dslik/ttam/stamps/1071A/1071-0101/latest/pcb_top.png

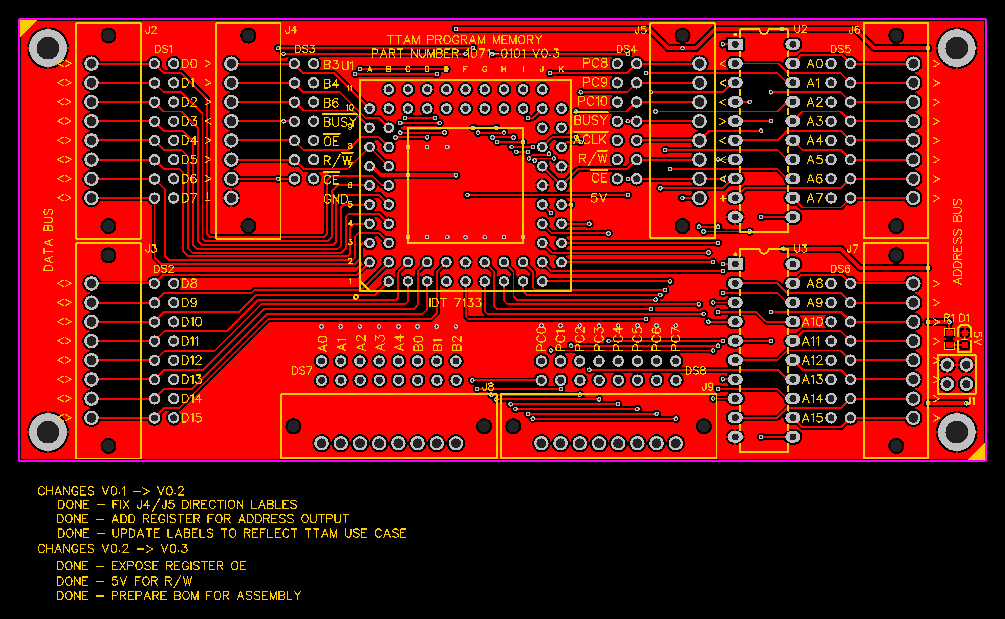
stamps/1071A/1071-0101/latest/pcb_top.png
