dslik/ttam/stamps/1072A/1072-0101/latest/pcb_top.png

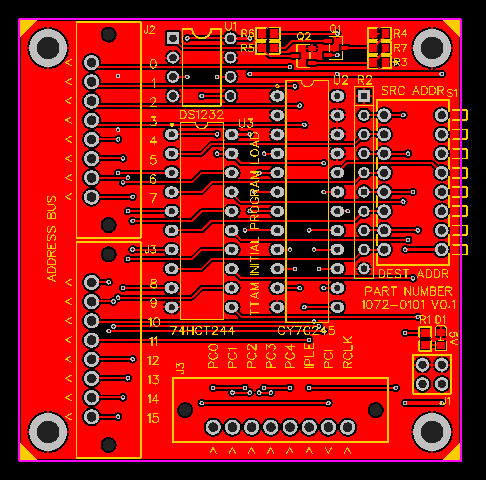
stamps/1072A/1072-0101/latest/pcb_top.png
