dslik/ttam/stamps/1073A/1073-0101/latest/pcb_top.png

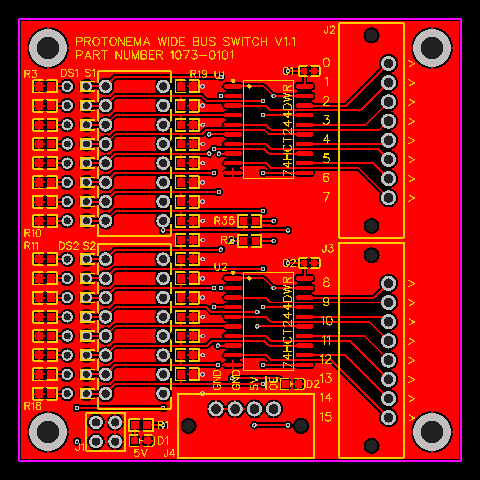
stamps/1073A/1073-0101/latest/pcb_top.png
