dslik/ttam/stamps/1074A/1074-0101/latest/pcb_top.png

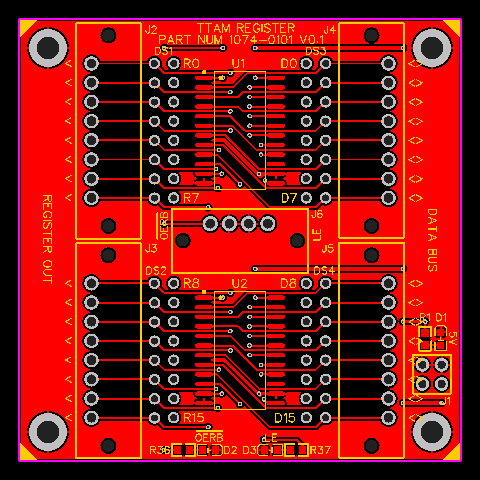
stamps/1074A/1074-0101/latest/pcb_top.png
