dslik/ttam/stamps/1075A/1075-0101/latest/pcb_top.png

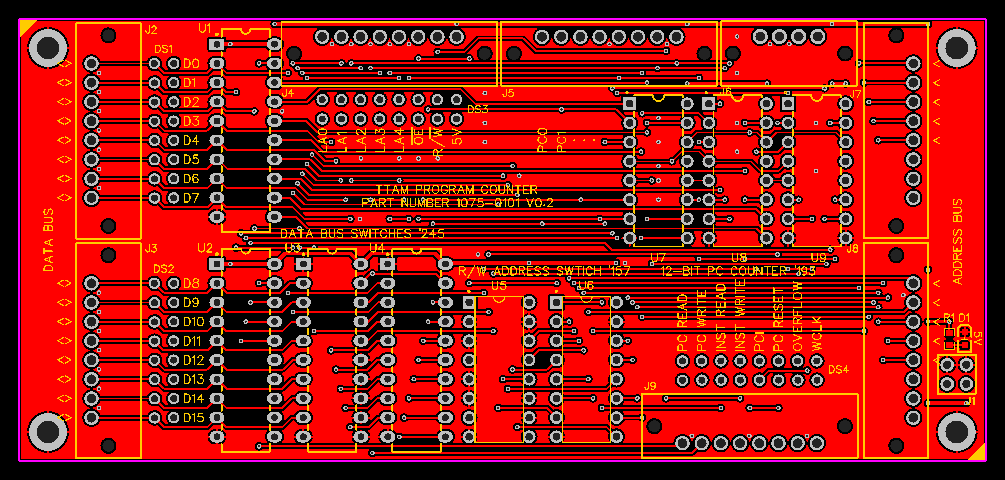
stamps/1075A/1075-0101/latest/pcb_top.png
