dslik/ttam/stamps/1076A/1076-0101/latest/pcb_top.png

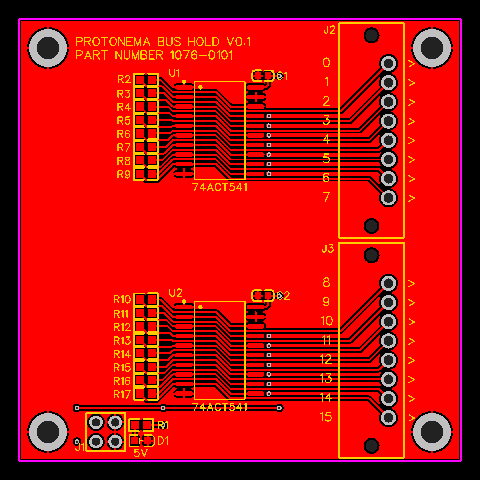
stamps/1076A/1076-0101/latest/pcb_top.png
