dslik/ttam/stamps/1077A/1077-0101/latest/pcb_top.png

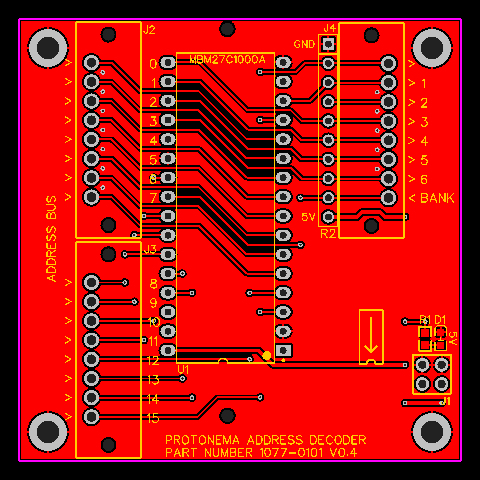
stamps/1077A/1077-0101/latest/pcb_top.png
