dslik/ttam/stamps/1078A/1078-0101/latest/pcb_top.png

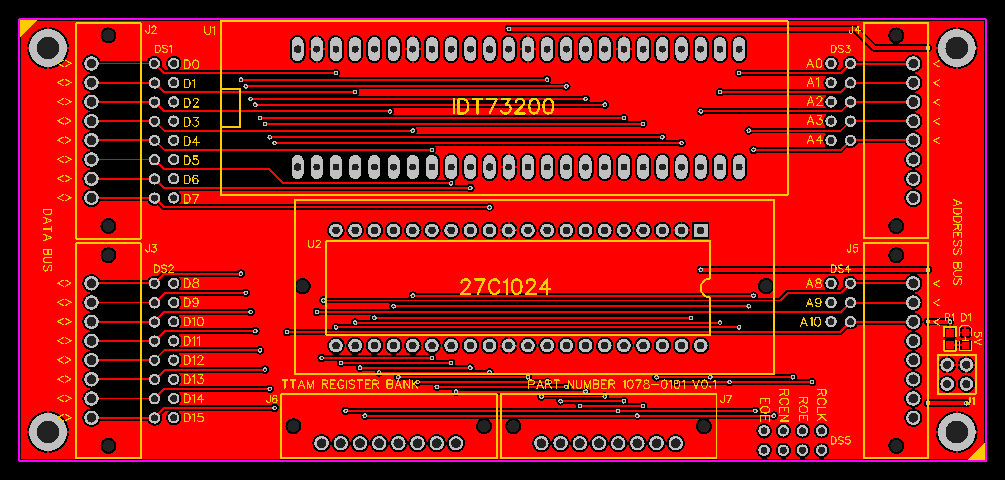
stamps/1078A/1078-0101/latest/pcb_top.png
