dslik/ttam/stamps/1079A/1079-0101/latest/pcb_top.png

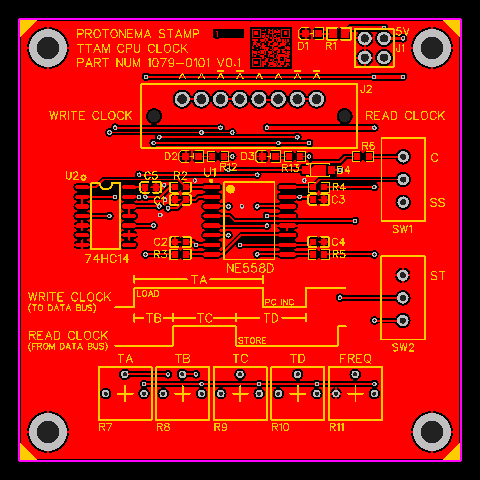
stamps/1079A/1079-0101/latest/pcb_top.png
