dslik/ttam/stamps/1080A/1080-0101/latest/pcb_bottom.png

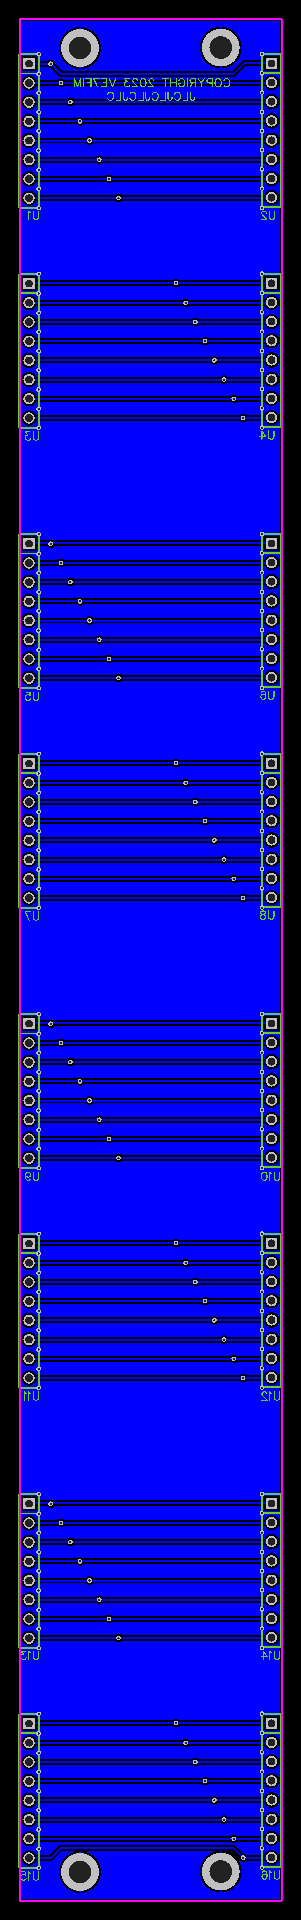
stamps/1080A/1080-0101/latest/pcb_bottom.png
