dslik/ttam/stamps/1080A/1080-0101/latest/pcb_top.png

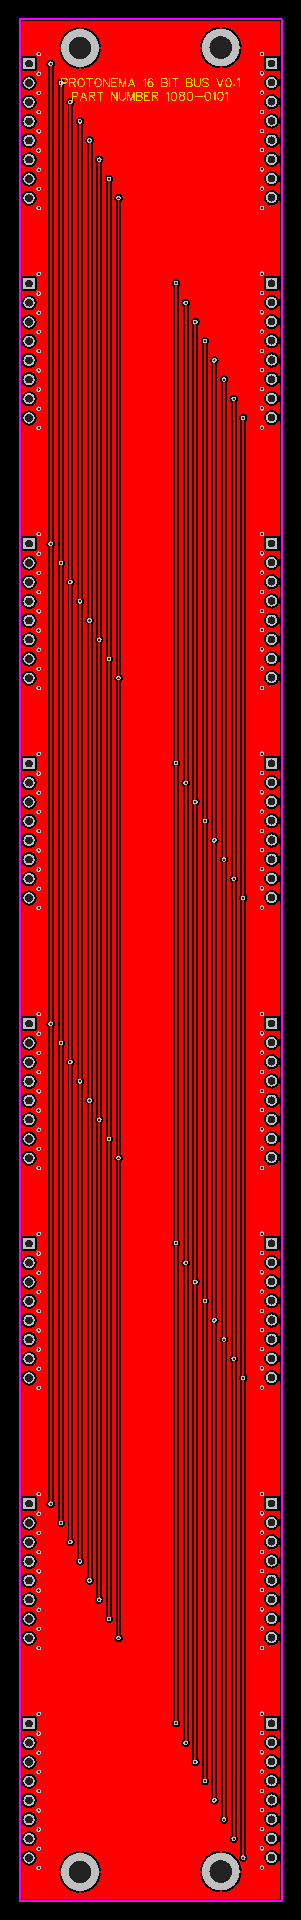
stamps/1080A/1080-0101/latest/pcb_top.png
